iamBVC/pocketDSP/KiCad_Project/pocketDSP.sch

## KiCad design KiCad_Project/pocketDSP.sch (2021-11-12)

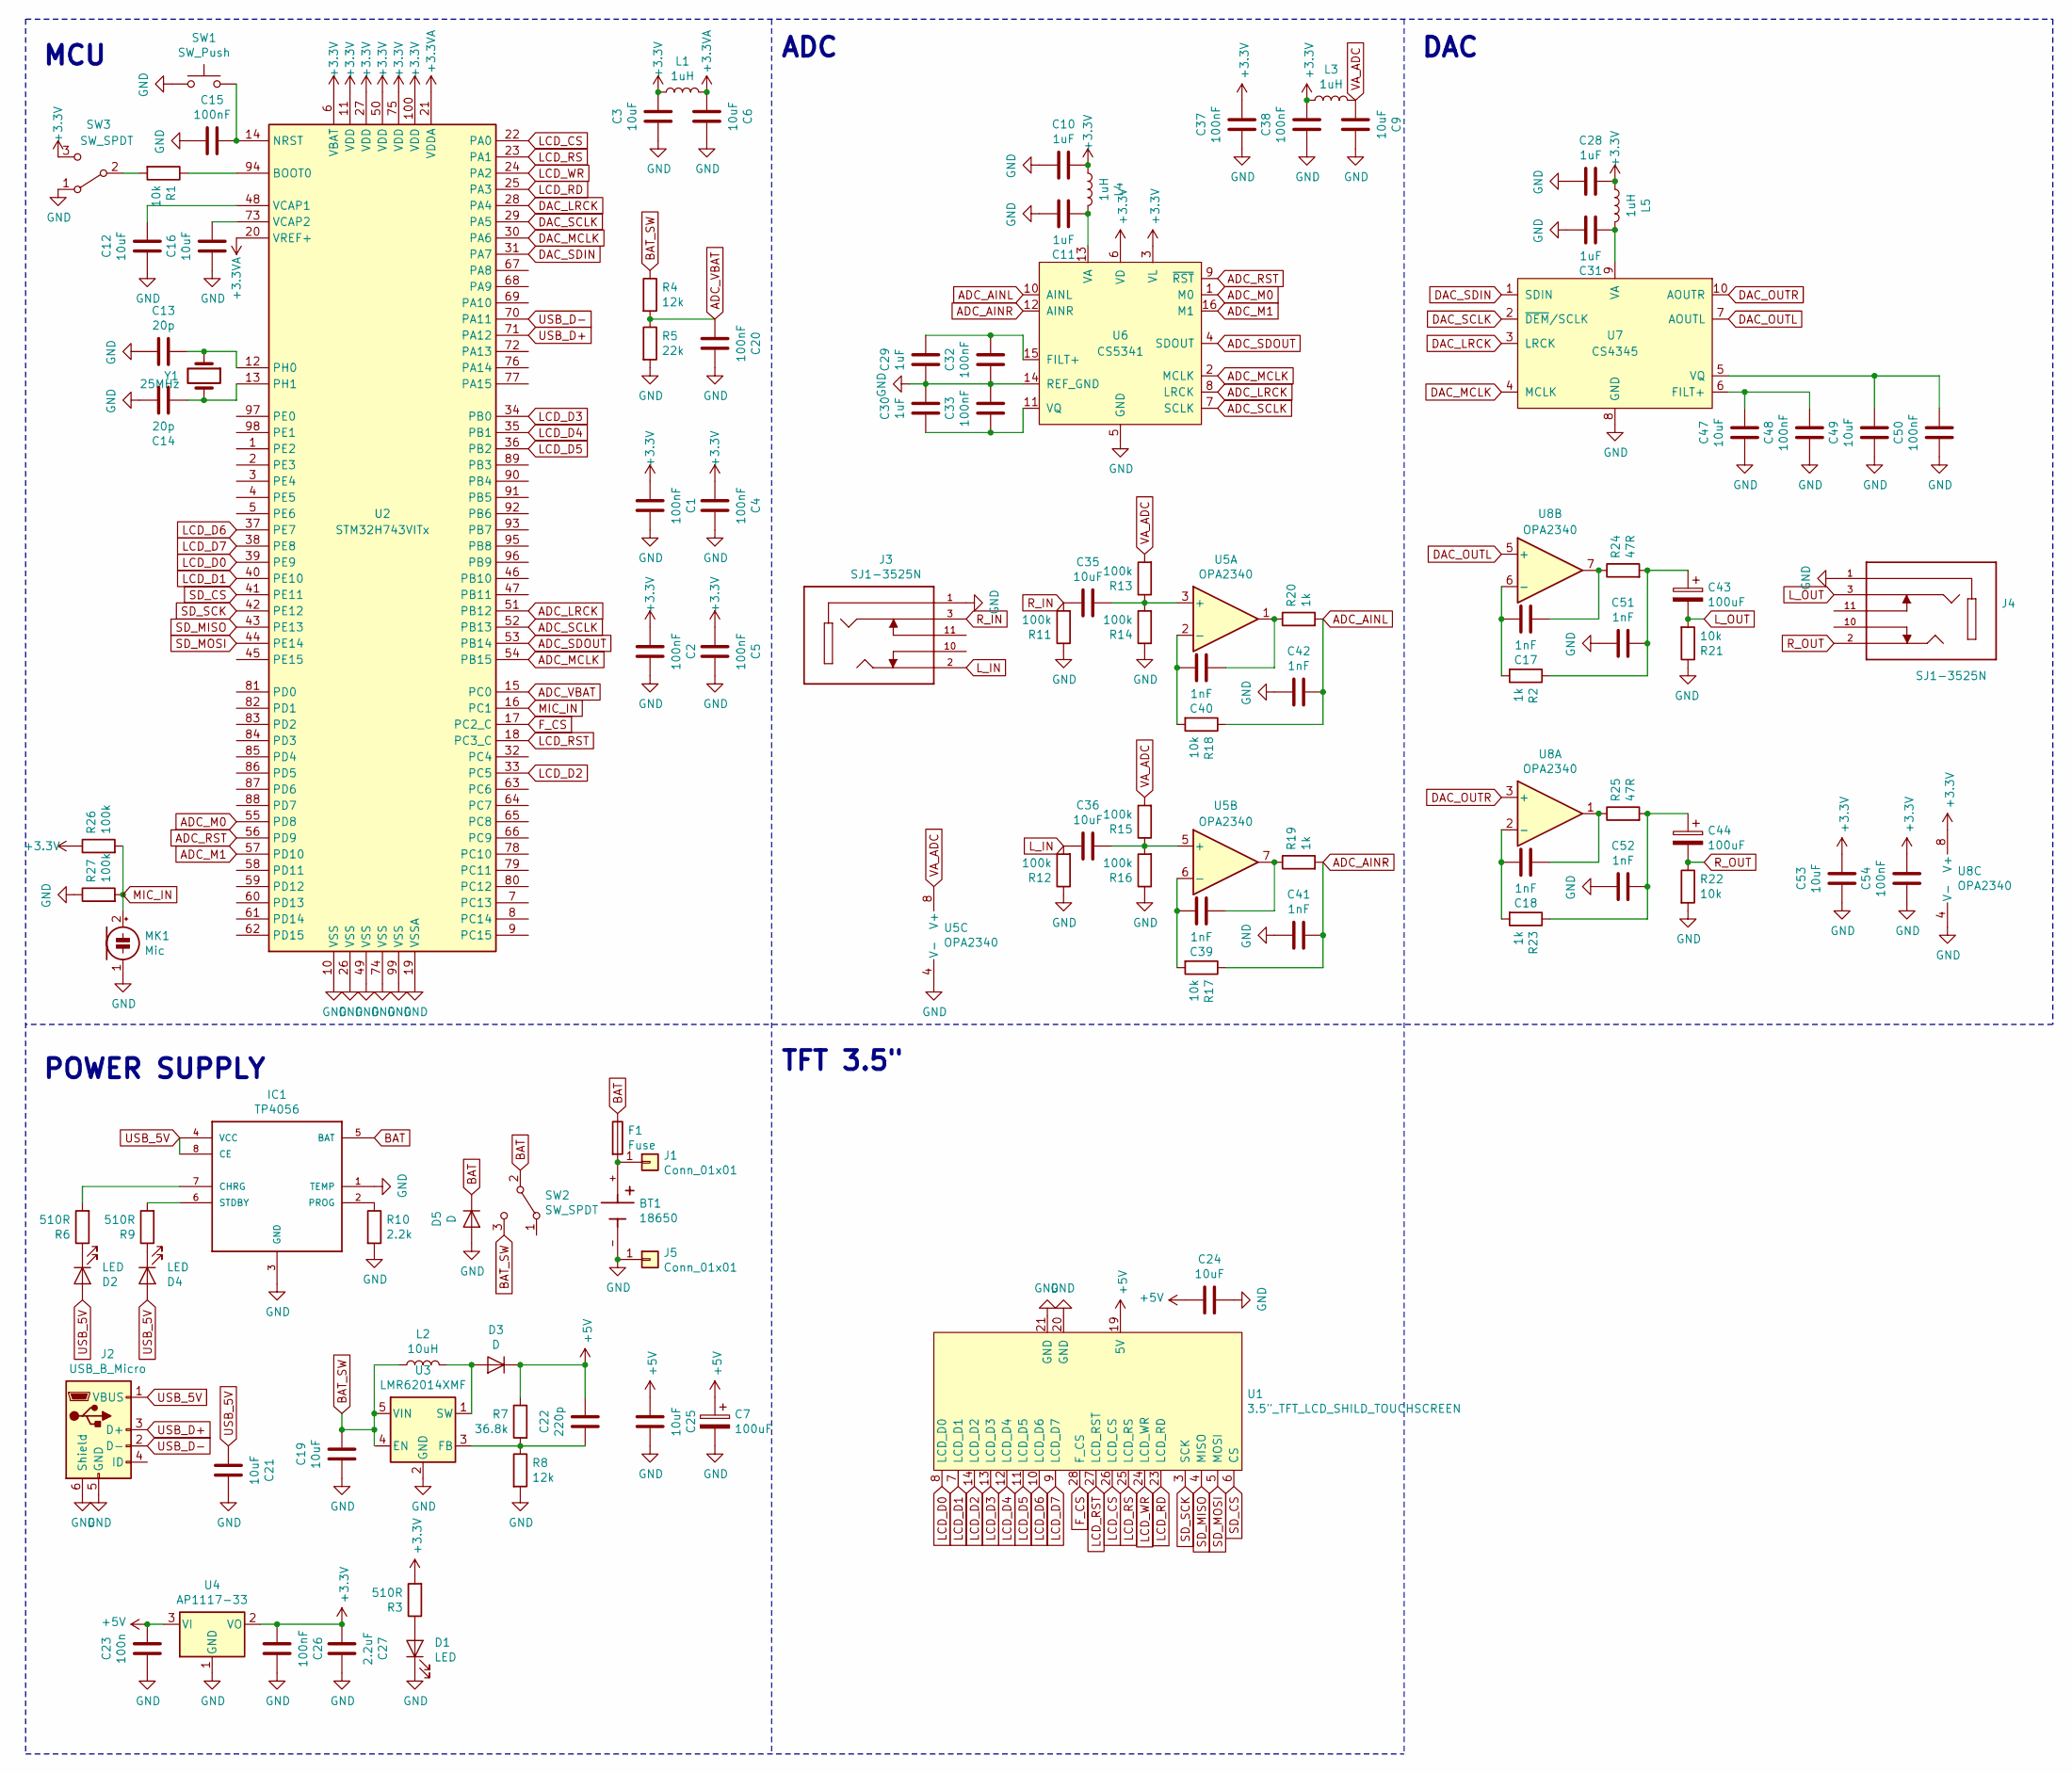
[picture p8: schematic pocketDSP.sch]

Parts:
BT1: 18650; BAT_BK-18650-PC2
C1, C2, C4, C5, C15, C20, C26, C32, C33, C37, C38, C48, C50, C54: 100nF; C_0805_2012Metric_Pad1.15x1.40mm_HandSolder
C3, C6, C9, C12, C16, C19, C21, C24, C25, C35, C36, C47, C49, C53: 10uF; C_0805_2012Metric_Pad1.15x1.40mm_HandSolder
C7, C43, C44: 100uF; CP_EIA-3216-18_Kemet-A_Pad1.58x1.35mm_HandSolder
C10, C11, C28, C29, C30, C31: 1uF; C_0805_2012Metric_Pad1.15x1.40mm_HandSolder
C13, C14: 20p; C_0805_2012Metric_Pad1.15x1.40mm_HandSolder
C17, C18, C39, C40, C41, C42, C51, C52: 1nF; C_0805_2012Metric_Pad1.15x1.40mm_HandSolder
C22: 220p; C_0805_2012Metric_Pad1.15x1.40mm_HandSolder
C23: 100n; C_0805_2012Metric_Pad1.15x1.40mm_HandSolder
C27: 2.2uF; C_0805_2012Metric_Pad1.15x1.40mm_HandSolder
D1, D2, D4: LED; LED_0805_2012Metric
D3: D; D_SOD-123
D5: D; D_SMC_Handsoldering
F1: Fuse; Littelfuse_Inc-0155-0-0-MFG
IC1: TP4056; SOIC-8-1EP_3.9x4.9mm_P1.27mm_EP2.29x3mm_ThermalVias
J1, J5: Conn_01x01; TestPoint_Pad_3.0x3.0mm
J2: USB_B_Micro; USB_Micro-B_Wuerth_629105150521
J3, J4: SJ1-3525N; CUI_SJ1-3525N
L1, L3, L4, L5: 1uH; L_0805_2012Metric_Pad1.15x1.40mm_HandSolder
L2: 10uH; L_Coilcraft_LPS5030
MK1: Mic; CUI_CMA-6542PF
R1, R17, R18, R21, R22: 10k; R_0805_2012Metric_Pad1.15x1.40mm_HandSolder
R2, R19, R20, R23: 1k; R_0805_2012Metric_Pad1.15x1.40mm_HandSolder
R3, R6, R9: 510R; R_0805_2012Metric_Pad1.15x1.40mm_HandSolder
R4, R8: 12k; R_0805_2012Metric_Pad1.15x1.40mm_HandSolder
R5: 22k; R_0805_2012Metric_Pad1.15x1.40mm_HandSolder
R7: 36.8k; R_0805_2012Metric_Pad1.15x1.40mm_HandSolder
R10: 2.2k; R_0805_2012Metric_Pad1.15x1.40mm_HandSolder
R11, R12, R13, R14, R15, R16, R26, R27: 100k; R_0805_2012Metric_Pad1.15x1.40mm_HandSolder
R24, R25: 47R; R_0805_2012Metric_Pad1.15x1.40mm_HandSolder
SW1: SW_Push; SW_SPST_CK_KXT3
SW2, SW3: SW_SPDT; SW_SPDT_PCM12
U1: 3.5\"_TFT_LCD_SHILD_TOUCHSCREEN; 3.5inch TFT LCD SHIELD
U2: STM32H743VITx; LQFP-100_14x14mm_P0.5mm
U3: LMR62014XMF; SOT-23-5
U4: AP1117-33; SOT-223-3_TabPin2
U5, U8: OPA2340; SOIC-8_3.9x4.9mm_P1.27mm
U6: CS5341; TSSOP-16_4.4x5mm_P0.65mm
U7: CS4345; TSSOP-10_3x3mm_P0.5mm
Y1: 25MHz; Crystal_SMD_5032-2Pin_5.0x3.2mm_HandSoldering

Connections:
+3.3V: C1.2, C2.2, C3.1, C4.2, C5.2, C10.1, C26.2, C27.2, C28.1, C37.1, C38.1, C53.1, C54.1, L1.1, L3.1, L4.1, L5.1, R3.2, R26.1, SW3.3 (C), U2.6 (VBAT), U2.11 (VDD), U2.27 (VDD), U2.50 (VDD), U2.75 (VDD), U2.100 (VDD), U4.2 (VO), U6.3 (VL), U6.6 (VD), U8.8 (V+)
+3.3VA: C6.2, L1.2, U2.20 (VREF+), U2.21 (VDDA)
+5V: C7.1, C22.2, C23.1, C24.1, C25.1, D3.1 (K), R7.1, U1.19 (5V), U4.3 (VI)
ADC_AINL: C42.2, R18.1, R20.2, U6.10 (AINL)
ADC_AINR: C41.2, R17.1, R19.2, U6.12 (AINR)
ADC_LRCK: U2.51 (PB12), U6.8 (LRCK)
ADC_M0: U2.55 (PD8), U6.1 (M0)
ADC_M1: U2.57 (PD10), U6.16 (M1)
ADC_MCLK: U2.54 (PB15), U6.2 (MCLK)
ADC_RST: U2.56 (PD9), U6.9 (~RST)
ADC_SCLK: U2.52 (PB13), U6.7 (SCLK)
ADC_SDOUT: U2.53 (PB14), U6.4 (SDOUT)
ADC_VBAT: C20.2, R4.2, R5.1, U2.15 (PC0)
BAT: D5.1 (K), F1.1, IC1.5 (BAT), SW2.2 (B)
BAT_SW: C19.1, L2.1, R4.1, SW2.3 (C), U3.4 (EN), U3.5 (VIN)
DAC_LRCK: U2.28 (PA4), U7.3 (LRCK)
DAC_MCLK: U2.30 (PA6), U7.4 (MCLK)
DAC_OUTL: U7.7 (AOUTL), U8.5 (+)
DAC_OUTR: U7.10 (AOUTR), U8.3 (+)
DAC_SCLK: U2.29 (PA5), U7.2 (~DEM~/SCLK)
DAC_SDIN: U2.31 (PA7), U7.1 (SDIN)
F_CS: U1.28 (F_CS), U2.17 (PC2_C)
GND: BT1.-, C1.1, C2.1, C3.2, C4.1, C5.1, C6.1, C7.2, C9.1, C10.2, C11.1, C12.2, C13.2, C14.1, C15.2, C16.2, C19.2, C20.1, C21.1, C23.2, C24.2, C25.2, C26.1, C27.1, C28.2, C29.2, C30.1, C31.1, C32.2, C33.1, C37.2, C38.2, C41.1, C42.1, C47.2, C48.2, C49.2, C50.2, C51.1, C52.1, C53.2, C54.2, D1.1 (K), D5.2 (A), IC1.1 (TEMP), IC1.3 (GND), J2.5 (GND), J2.6 (Shield), J3.1, J4.1, J5.1, MK1.1 (-), R5.2, R8.2, R10.2, R11.1, R12.1, R14.1, R16.1, R21.1, R22.2, R27.1, SW1.1, SW3.1 (A), U1.20 (GND), U1.21 (GND), U2.10 (VSS), U2.19 (VSSA), U2.26 (VSS), U2.49 (VSS), U2.74 (VSS), U2.99 (VSS), U3.2 (GND), U4.1 (GND), U5.4 (V-), U6.5 (GND), U6.14 (REF_GND), U7.8 (GND), U8.4 (V-)
LCD_CS: U1.26 (LCD_CS), U2.22 (PA0)
LCD_D0: U1.8 (LCD_D0), U2.39 (PE9)
LCD_D1: U1.7 (LCD_D1), U2.40 (PE10)
LCD_D2: U1.14 (LCD_D2), U2.33 (PC5)
LCD_D3: U1.13 (LCD_D3), U2.34 (PB0)
LCD_D4: U1.12 (LCD_D4), U2.35 (PB1)
LCD_D5: U1.11 (LCD_D5), U2.36 (PB2)
LCD_D6: U1.10 (LCD_D6), U2.37 (PE7)
LCD_D7: U1.9 (LCD_D7), U2.38 (PE8)
LCD_RD: U1.23 (LCD_RD), U2.25 (PA3)
LCD_RS: U1.25 (LCD_RS), U2.23 (PA1)
LCD_RST: U1.27 (LCD_RST), U2.18 (PC3_C)
LCD_WR: U1.24 (LCD_WR), U2.24 (PA2)
L_IN: C36.2, J3.2, R12.2
L_OUT: C43.2, J4.3, R21.2
MIC_IN: MK1.2 (+), R26.2, R27.2, U2.16 (PC1)
unnamed: BT1.+, F1.2, J1.1
unnamed: C11.2, L4.2, U6.13 (VA)
unnamed: C12.1, U2.48 (VCAP1)
unnamed: C13.1, U2.12 (PH0), Y1.1
unnamed: C14.2, U2.13 (PH1), Y1.2
unnamed: C15.1, SW1.2, U2.14 (NRST)
unnamed: C16.1, U2.73 (VCAP2)
unnamed: C17.1, R24.1, U8.7
unnamed: C17.2, R2.2, U8.6 (-)
unnamed: C18.1, R25.1, U8.1
unnamed: C18.2, R23.2, U8.2 (-)
unnamed: C22.1, R7.2, R8.1, U3.3 (FB)
unnamed: C29.1, C32.1, U6.15 (FILT+)
unnamed: C30.2, C33.2, U6.11 (VQ)
unnamed: C31.2, L5.2, U7.9 (VA)
unnamed: C35.1, R13.1, R14.2, U5.3 (+)
unnamed: C36.1, R15.1, R16.2, U5.5 (+)
unnamed: C39.1, R19.1, U5.7
unnamed: C39.2, R17.2, U5.6 (-)
unnamed: C40.1, R20.1, U5.1
unnamed: C40.2, R18.2, U5.2 (-)
unnamed: C43.1, C51.2, R2.1, R24.2
unnamed: C44.1, C52.2, R23.1, R25.2
unnamed: C47.1, C48.1, U7.6 (FILT+)
unnamed: C49.1, C50.1, U7.5 (VQ)
unnamed: D1.2 (A), R3.1
unnamed: D2.1 (K), R6.1
unnamed: D3.2 (A), L2.2, U3.1 (SW)
unnamed: D4.1 (K), R9.1
unnamed: IC1.2 (PROG), R10.1
unnamed: IC1.6 (STDBY), R9.2
unnamed: IC1.7 (CHRG), R6.2
unnamed: R1.1, U2.94 (BOOT0)
unnamed: R1.2, SW3.2 (B)
R_IN: C35.2, J3.3, R11.2
R_OUT: C44.2, J4.2, R22.1
SD_CS: U1.6 (CS), U2.41 (PE11)
SD_MISO: U1.4 (MISO), U2.43 (PE13)
SD_MOSI: U1.5 (MOSI), U2.44 (PE14)
SD_SCK: U1.3 (SCK), U2.42 (PE12)
USB_5V: C21.2, D2.2 (A), D4.2 (A), IC1.4 (VCC), IC1.8 (CE), J2.1 (VBUS)
USB_D+: J2.3 (D+), U2.71 (PA12)
USB_D-: J2.2 (D-), U2.70 (PA11)
VA_ADC: C9.2, L3.2, R13.2, R15.2, U5.8 (V+)

Notes on the sheet:
MCU
POWER SUPPLY
DAC
ADC
TFT 3.5"
