iamBVC/pocketDSP/STM32_Project/Core/Inc/tft.h

#include "stdint.h"
#include "lvgl/lvgl.h"
  
#define true	1
#define false	0

#define	BLACK   0x0000
#define	BLUE    0x001F
#define	RED     0xF800
#define	GREEN   0x07E0
#define CYAN    0x07FF
#define MAGENTA 0xF81F
#define YELLOW  0xFFE0
#define WHITE   0xFFFF

#define MIPI_DCS_REV1   (1<<0)
#define AUTO_READINC    (1<<1)
#define READ_BGR        (1<<2)
#define READ_LOWHIGH    (1<<3)
#define READ_24BITS     (1<<4)
#define XSA_XEA_16BIT   (1<<5)
#define READ_NODUMMY    (1<<6)
#define INVERT_GS       (1<<8)
#define INVERT_SS       (1<<9)
#define MV_AXIS         (1<<10)
#define INVERT_RGB      (1<<11)
#define REV_SCREEN      (1<<12)
#define FLIP_VERT       (1<<13)
#define FLIP_HORIZ      (1<<14)

void tft_init(uint16_t ID);
void reset(void);
uint16_t readID(void);
void setRotation(uint8_t r);
void invertDisplay(uint8_t i);
void vertScroll(int16_t top, int16_t scrollines, int16_t offset);
void setTextWrap(uint8_t w);
void setTextColor (uint16_t color);
void setTextSize (uint8_t size);
void setCursor(int16_t x, int16_t y);
void printstr (uint8_t *str);
void drawPixel(int16_t x, int16_t y, uint16_t color);
void fillScreen(uint16_t color);
void fillRect(int16_t x, int16_t y, int16_t w, int16_t h, uint16_t color);
void drawLine(int16_t x0, int16_t y0, int16_t x1, int16_t y1, uint16_t color);
void drawRect(int16_t x, int16_t y, int16_t w, int16_t h, uint16_t color);
void drawCircle(int16_t x0, int16_t y0, int16_t r, uint16_t color);
void drawCircleHelper(int16_t x0, int16_t y0, int16_t r, uint8_t cornername, uint16_t color);
void fillCircle(int16_t x0, int16_t y0, int16_t r, uint16_t color);
void fillCircleHelper(int16_t x0, int16_t y0, int16_t r, uint8_t cornername, int16_t delta, uint16_t color);
void drawTriangle(int16_t x0, int16_t y0, int16_t x1, int16_t y1, int16_t x2, int16_t y2, uint16_t color);
void fillTriangle(int16_t x0, int16_t y0, int16_t x1, int16_t y1, int16_t x2, int16_t y2, uint16_t color);
void drawRoundRect(int16_t x0, int16_t y0, int16_t w, int16_t h, int16_t radius, uint16_t color);
void fillRoundRect(int16_t x0, int16_t y0, int16_t w, int16_t h, int16_t radius, uint16_t color);
//void drawBitmap(int16_t x, int16_t y, const uint8_t bitmap[], int16_t w, int16_t h, uint16_t color);
//void drawBitmap(int16_t x, int16_t y, const uint8_t bitmap[], int16_t w, int16_t h, uint16_t color, uint16_t bg);
void drawBitmap(int16_t x, int16_t y, uint8_t *bitmap, int16_t w, int16_t h, uint16_t color);
void drawBitmapbg(int16_t x, int16_t y, uint8_t *bitmap, int16_t w, int16_t h, uint16_t color, uint16_t bg);
//void drawXBitmap(int16_t x, int16_t y, const uint8_t bitmap[], int16_t w, int16_t h, uint16_t color);
//void drawGrayscaleBitmap(int16_t x, int16_t y, const uint8_t bitmap[], int16_t w, int16_t h);
void drawGrayscaleBitmap(int16_t x, int16_t y, uint8_t *bitmap, int16_t w, int16_t h);
//void drawGrayscaleBitmap(int16_t x, int16_t y, const uint8_t bitmap[], const uint8_t mask[], int16_t w, int16_t h);
void drawGrayscaleBitmapmask(int16_t x, int16_t y, uint8_t *bitmap, uint8_t *mask, int16_t w, int16_t h);
//void drawRGBBitmap(int16_t x, int16_t y, const uint16_t bitmap[], int16_t w, int16_t h);
void drawRGBBitmap(int16_t x, int16_t y, uint16_t *bitmap, int16_t w, int16_t h);
//void drawRGBBitmap(int16_t x, int16_t y, const uint16_t bitmap[], const uint8_t mask[], int16_t w, int16_t h);
void drawRGBBitmapmask(int16_t x, int16_t y, uint16_t *bitmap, uint8_t *mask, int16_t w, int16_t h);
void testFastLines(uint16_t color1, uint16_t color2);
void testLines(uint16_t color);
void testFillScreen();
void testRects(uint16_t color);
void testFilledRects(uint16_t color1, uint16_t color2);
void testFilledCircles(uint8_t radius, uint16_t color) ;
void testCircles(uint8_t radius, uint16_t color);
void testFilledRoundRects();
void testRoundRects();
void testFilledTriangles();
void testTriangles();
void scrollup (uint16_t speed);
void scrolldown (uint16_t speed);
void readTouch(uint16_t *x, uint16_t *y, uint16_t *z);
void drawScreen(uint16_t *data, lv_area_t *area);
