iamBVC/pocketDSP/STM32_Project/Core/Inc/freq_response.h

/*
 * freq_response.h
 *
 *  Created on: 4 ott 2021
 *      Author: Brian
 */

#ifndef INC_FREQ_RESPONSE_H_
#define INC_FREQ_RESPONSE_H_

#include "system.h"

void start_freqresp();
void freqresp_sample_callback();

#endif /* INC_FREQ_RESPONSE_H_ */
